cdhutch/cad/gridfinity/source/tooltrace/wera-454-7-hf-set-1/photos/small.jpeg

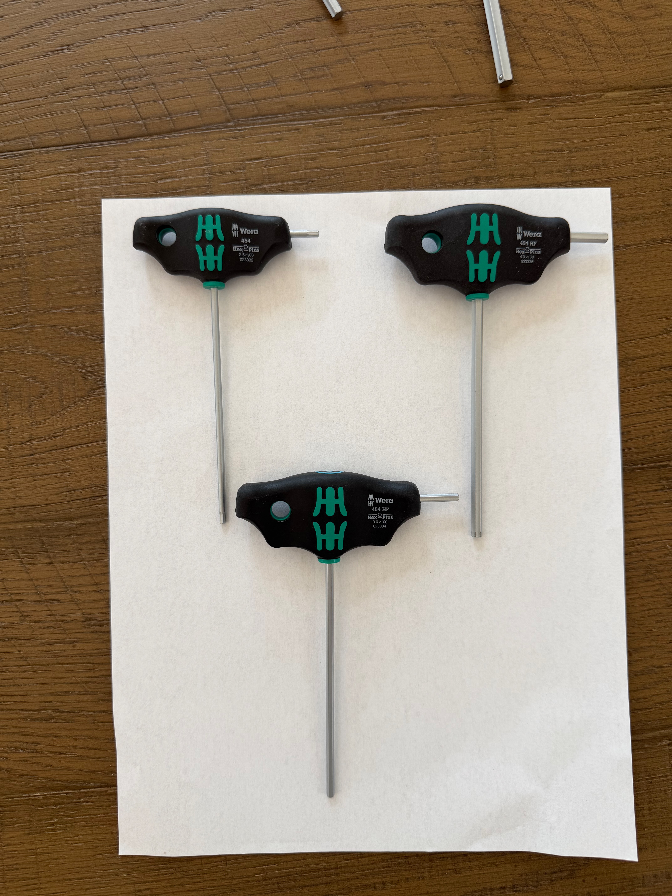
gridfinity/source/tooltrace/wera-454-7-hf-set-1/photos/small.jpeg
